Zubax/canface_cf1/firmware/src/board/board.cpp

/*
 * Copyright (C) 2015  Zubax Robotics  <info@zubax.com>
 *
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
 * Author: Pavel Kirienko <pavel.kirienko@zubax.com>
 */

#include "board.hpp"
#include <cstring>
#include <ch.hpp>
#include <hal.h>
#include <unistd.h>
#include <zubax_chibios/platform/stm32/flash_writer.hpp>

/// PAL setup
const ::PALConfig pal_default_config =
{
#if STM32_HAS_GPIOA
    {VAL_GPIOA_MODER,VAL_GPIOA_OTYPER,VAL_GPIOA_OSPEEDR,VAL_GPIOA_PUPDR,VAL_GPIOA_ODR,VAL_GPIOA_AFRL,VAL_GPIOA_AFRH},
#endif
#if STM32_HAS_GPIOB
    {VAL_GPIOB_MODER,VAL_GPIOB_OTYPER,VAL_GPIOB_OSPEEDR,VAL_GPIOB_PUPDR,VAL_GPIOB_ODR,VAL_GPIOB_AFRL,VAL_GPIOB_AFRH},
#endif
#if STM32_HAS_GPIOC
    {VAL_GPIOC_MODER,VAL_GPIOC_OTYPER,VAL_GPIOC_OSPEEDR,VAL_GPIOC_PUPDR,VAL_GPIOC_ODR,VAL_GPIOC_AFRL,VAL_GPIOC_AFRH},
#endif
#if STM32_HAS_GPIOD
    {VAL_GPIOD_MODER,VAL_GPIOD_OTYPER,VAL_GPIOD_OSPEEDR,VAL_GPIOD_PUPDR,VAL_GPIOD_ODR,VAL_GPIOD_AFRL,VAL_GPIOD_AFRH},
#endif
#if STM32_HAS_GPIOE
    {VAL_GPIOE_MODER,VAL_GPIOE_OTYPER,VAL_GPIOE_OSPEEDR,VAL_GPIOE_PUPDR,VAL_GPIOE_ODR,VAL_GPIOE_AFRL,VAL_GPIOE_AFRH},
#endif
#if STM32_HAS_GPIOF
    {VAL_GPIOF_MODER,VAL_GPIOF_OTYPER,VAL_GPIOF_OSPEEDR,VAL_GPIOF_PUPDR,VAL_GPIOF_ODR,VAL_GPIOF_AFRL,VAL_GPIOF_AFRH}
#endif
};

/// Provided by linker
const extern std::uint8_t DeviceSignatureStorage[];

namespace board
{
namespace
{

constexpr float ADCVref = 3.3F;
constexpr unsigned ADCResolution = 12;


void initADC()
{
    os::CriticalSectionLocker cs_locker;

    RCC->APB2ENR  |=  RCC_APB2ENR_ADC1EN;
    RCC->APB2RSTR |=  RCC_APB2RSTR_ADC1RST;
    RCC->APB2RSTR &= ~RCC_APB2RSTR_ADC1RST;

    // RSTCAL
    ASSERT_ALWAYS(!(ADC1->CR2 & ADC_CR2_RSTCAL));
    ADC1->CR2 = ADC_CR2_ADON | ADC_CR2_RSTCAL;
    while (ADC1->CR2 & ADC_CR2_RSTCAL) { }

    // CAL
    ASSERT_ALWAYS(!(ADC1->CR2 & ADC_CR2_CAL));
    ADC1->CR2 = ADC_CR2_ADON | ADC_CR2_CAL;
    while (ADC1->CR2 & ADC_CR2_CAL) { }

    // SQR are inited correctly by default

    // Channel 0 max sample time (239.5 cycles)
    ADC1->SMPR2 = ADC_SMPR2_SMP0_0 | ADC_SMPR2_SMP0_1 | ADC_SMPR2_SMP0_2;

    // Start in continuous scan mode (free-running)
    ADC1->CR1 = ADC_CR1_SCAN;
    ADC1->CR2 = ADC_CR2_ADON | ADC_CR2_CONT | ADC_CR2_EXTTRIG |
                ADC_CR2_EXTSEL_0 | ADC_CR2_EXTSEL_1 | ADC_CR2_EXTSEL_2 | ADC_CR2_SWSTART;
}

}

os::watchdog::Timer init(unsigned watchdog_timeout_msec, os::config::Param<unsigned>& cfg_uart_baudrate)
{
    /*
     * OS initialization first
     */
    halInit();
    chSysInit();

    /*
     * Watchdog
     */
    os::watchdog::init();
    os::watchdog::Timer wdt;
    wdt.startMSec(watchdog_timeout_msec);

    /*
     * Configuration manager
     */
    const int config_init_res = os::config::init();
    if (config_init_res < 0)
    {
        die();
    }

    /*
     * ADC
     */
    initADC();

    /*
     * Serial port
     */
    reconfigureUART(cfg_uart_baudrate.get());

    /*
     * Prompt
     */
    os::lowsyslog(PRODUCT_NAME_STRING " %d.%d.%08x / %d %s\n",
                  FW_VERSION_MAJOR, FW_VERSION_MINOR, GIT_HASH, config_init_res,
                  watchdogTriggeredLastReset() ? "WDTRESET" : "OK");
    return wdt;
}

void reconfigureUART(const unsigned baudrate)
{
    static SerialConfig config =
    {
        0,
        0,
        USART_CR2_STOP1_BITS,
        0
    };

    if (baudrate != config.speed)
    {
        config.speed = baudrate;
        sdStart(&STDOUT_SD, &config);
    }
}

__attribute__((noreturn))
void die()
{
    while (1)
    {
        setStatusLED(false);
        setTrafficLED(false);
        ::usleep(25000);
        setStatusLED(true);
        setTrafficLED(true);
        ::usleep(25000);
    }
}

void restart()
{
    NVIC_SystemReset();
}

void setStatusLED(bool state)
{
    palWritePad(GPIOE, GPIOE_LED_STATUS, std::uint8_t(!state));
}

void setTrafficLED(bool state)
{
    palWritePad(GPIOE, GPIOE_LED_TRAFFIC, std::uint8_t(!state));
}

void enableCANPower(bool state)
{
    palWritePad(GPIOA, GPIOA_CAN_POWER_DIS, std::uint8_t(!state));
    palWritePad(GPIOB, GPIOB_LED_CAN_POWER_DIS, std::uint8_t(!state));
}

void enableCANTerminator(bool state)
{
    palWritePad(GPIOB, GPIOB_CAN_TERMINATOR_EN, std::uint8_t(state));
}

float getBusVoltage()
{
    static constexpr float DivisionRatio = 2;
    // The values are arranged with numerical stability in mind
    return float(ADC1->DR) * DivisionRatio * ADCVref / float((1U << ADCResolution) - 1U);
}

UniqueID readUniqueID()
{
    UniqueID bytes;
    std::fill(bytes.begin(), bytes.end(), 0);
    std::memcpy(bytes.data(), reinterpret_cast<const void*>(0x1FFFF7AC), 12);
    return bytes;
}

bool tryReadDeviceSignature(DeviceSignature& out_sign)
{
    std::memcpy(out_sign.data(), &DeviceSignatureStorage[0], std::tuple_size<DeviceSignature>::value);
    for (auto x : out_sign)
    {
        if (x != 0xFF && x != 0x00)          // All 0xFF/0x00 is not a valid signature, it's empty storage
        {
            return true;
        }
    }
    return false;
}

bool tryWriteDeviceSignature(const DeviceSignature& sign)
{
    {
        DeviceSignature dummy;
        if (tryReadDeviceSignature(dummy))
        {
            return false;               // Already written
        }
    }

    // Before flash can be written, the source must be aligned.
    alignas(4) std::uint8_t aligned_buffer[std::tuple_size<DeviceSignature>::value];
    std::copy(std::begin(sign), std::end(sign), std::begin(aligned_buffer));

    os::stm32::FlashWriter writer;

    return writer.write(&DeviceSignatureStorage[0], &aligned_buffer[0], sizeof(aligned_buffer));
}

HardwareVersion detectHardwareVersion()
{
    auto v = HardwareVersion();

    v.major = HW_VERSION_MAJOR;
    v.minor = 0;                // Some detection will be added in future versions

    return v;
}

} // namespace board

namespace os
{

void applicationHaltHook()
{
    board::setStatusLED(true);
    board::setTrafficLED(true);
}

}

/*
 * Early init from ChibiOS
 */
extern "C"
{

void __early_init(void)
{
    stm32_clock_init();
}

void boardInit(void)
{
}

}
