Zubax/canface_cf1/bootloader/src/main.cpp

/*
 * Copyright (C) 2015  Zubax Robotics  <info@zubax.com>
 *
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
 * Author: Pavel Kirienko <pavel.kirienko@zubax.com>
 */

#include <ch.hpp>
#include <hal.h>
#include <unistd.h>
#include <cstring>
#include <cstdio>
#include <cstdlib>
#include <zubax_chibios/os.hpp>
#include <zubax_chibios/platform/stm32/flash_writer.hpp>
#include <zubax_chibios/bootloader/bootloader.hpp>

#include "board/board.hpp"
#include "usb_cdc.hpp"
#include "cli.hpp"
#include "bootloader_app_interface.hpp"


namespace app
{
namespace
{
/**
 * This watchdog timeout will be applied to the bootloader itself, and also to the application boot process.
 * In other words, the application will have to reset the watchdog in this time after boot.
 */
constexpr unsigned WatchdogTimeoutMSec = 5000;

/**
 * This class contains logic and hardcoded values that are SPECIFIC FOR THIS PARTICULAR MCU AND APPLICATION.
 */
class AppStorageBackend : public bootloader::IAppStorageBackend
{
    static constexpr unsigned FlashPageSize = 2048;
    static constexpr unsigned ApplicationAddress = FLASH_BASE + APPLICATION_OFFSET;

    static unsigned getFlashSize()
    {
        return 1024 * *reinterpret_cast<std::uint16_t*>(0x1FFFF7CC);
    }

    static bool correctOffsetAndSize(std::size_t& offset, std::size_t& size)
    {
        const auto flash_end = FLASH_BASE + getFlashSize();
        offset += ApplicationAddress;
        if (offset >= flash_end)
        {
            return false;
        }
        if ((offset + size) >= flash_end)
        {
            size = flash_end - offset;
        }
        return true;
    }

public:
    static constexpr std::int16_t ErrEraseFailed = 9001;
    static constexpr std::int16_t ErrWriteFailed = 9002;

    int beginUpgrade()   override { return 0; }
    int endUpgrade(bool) override { return 0; }

    int write(std::size_t offset, const void* data, std::size_t size) override
    {
        if (!correctOffsetAndSize(offset, size))
        {
            return 0;
        }
        os::stm32::FlashWriter writer;

        // Blank check byte-by-byte, erase page only if needed
        for (std::size_t blank_check_pos = offset; blank_check_pos < (offset + size); blank_check_pos++)
        {
            if (UNLIKELY(*reinterpret_cast<const std::uint8_t*>(blank_check_pos) != 0xFF))
            {
                DEBUG_LOG("Erasing page at %x\n", blank_check_pos);
                const bool ok = writer.erasePageAt(blank_check_pos);
                if (!ok)
                {
                    return -ErrEraseFailed;
                }
            }
        }

        // Write
        return writer.write(reinterpret_cast<const void*>(offset), data, size) ? size : -ErrWriteFailed;
    }

    int read(std::size_t offset, void* data, std::size_t size) override
    {
        if (!correctOffsetAndSize(offset, size))
        {
            return 0;
        }
        std::memmove(data, reinterpret_cast<const void*>(offset), size);
        return size;
    }
};


static inline std::pair<unsigned, unsigned> bootloaderStateToLEDOnOffDurationMSec(bootloader::State state)
{
    switch (state)
    {
    case bootloader::State::NoAppToBoot:
    {
        return {50, 50};
    }
    case bootloader::State::BootCancelled:
    {
        return {50, 950};
    }
    case bootloader::State::AppUpgradeInProgress:
    {
        return {500, 500};
    }
    case bootloader::State::BootDelay:
    case bootloader::State::ReadyToBoot:
    {
        return {0, 0};
    }
    }
    assert(false);
    return {0, 0};
}

}
}

int main()
{
    auto watchdog = board::init(app::WatchdogTimeoutMSec);

    chibios_rt::BaseThread::setPriority(LOWPRIO);

    /*
     * USB initialization
     */
    const auto uid = board::readUniqueID();

    usb_cdc::DeviceSerialNumber sn;
    std::fill(sn.begin(), sn.end(), 0);
    std::copy(uid.begin(), uid.end(), sn.begin());

    watchdog.reset();
    usb_cdc::init(sn);                  // Must not exceed watchdog timeout
    watchdog.reset();

    board::setStatusLED(true);

    /*
     * Bootloader logic initialization
     */
    app::AppStorageBackend backend;

    bootloader::Bootloader bl(backend);

    cli::init(bl);

    /*
     * Parsing the app shared struct
     */
    const auto app_shared = bootloader_app_interface::readAndErase();
    if (app_shared.second)
    {
        if (app_shared.first.stay_in_bootloader)
        {
            DEBUG_LOG("Boot cancelled by apps request\n");
            bl.cancelBoot();
        }
    }
    else
    {
        DEBUG_LOG("App shared struct not found\n");
    }

    /*
     * Main loop
     */
    while (!os::isRebootRequested())
    {
        watchdog.reset();

        const auto bl_state = bl.getState();
        if (bl_state == bootloader::State::ReadyToBoot)
        {
            break;
        }

        const auto duration = app::bootloaderStateToLEDOnOffDurationMSec(bl_state);
        if (duration.first == 0 && duration.second == 0)
        {
            board::setTrafficLED(false);
            chThdSleepMilliseconds(100);
        }
        else
        {
            board::setTrafficLED(true);
            chThdSleepMilliseconds(duration.first);
            board::setTrafficLED(false);
            chThdSleepMilliseconds(duration.second);
        }
    }

    watchdog.reset();

    if (os::isRebootRequested())
    {
        ::usleep(500000);       // Providing some time for other components to react
        board::restart();
    }

    /*
     * Booting the application
     */
    DEBUG_LOG("BOOTING APP\n");

    board::setTrafficLED(false);

    os::requestReboot();        // Notifying other components that we're going down

    ::usleep(500000);           // Providing some time for other components to react

    // Actually the state may have been switched, but it's ok for debugging
    assert(bl.getState() == bootloader::State::ReadyToBoot);

    watchdog.reset();           // The final reset, the application will have time to boot and init until next timeout

    board::bootApplication();
}


#define MATCH_GCC_VERSION(major, minor, patch)  \
    ((__GNUC__ == (major)) && (__GNUC_MINOR__ == (minor)) && (__GNUC_PATCHLEVEL__ == (patch)))

#if !(MATCH_GCC_VERSION(10, 3, 1))
# error "This compiler is not supported"
#endif
